Lnotti/5-Channel-High-Current-Li-po-Discharger/Solidworks/BoardV4.step

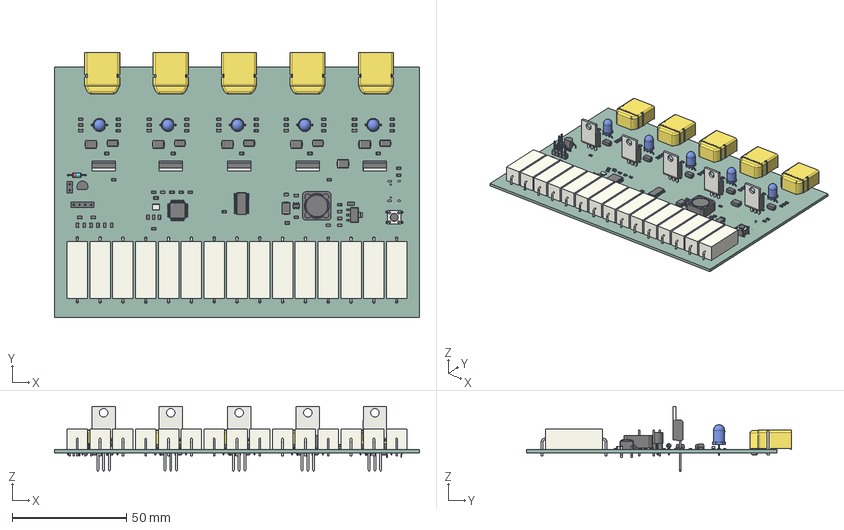
[picture p7: CAD file, 2026-05-29]
Solidworks/BoardV4.step
160.0 x 116.3 x 28.5 mm
C_0805_2012Metric x 23
XT60PW-M x 5
R_Axial_Power_L250mm_W90mm_P2794mm x 15
LED_D5.0mm-4_RGB_Wide_Pins x 5
R_0805_2012Metric x 44
D_SMB x 7
D_SMA x 5
SOT-223
TO-220-3_Vertical x 5
SW_PUSH_6mm
TO-92_Inline_Narrow
Crystal_SMD_3225-4Pin_3.2x2.5mm
PinHeader_1x04_P254mm_Vertical
LQFP-48_7x7mm_P0.5mm
Fuse_1206_3216Metric
SRR1260
TSOT-23-6
TSSOP-28_4.4x9.7mm_P0.65mm
D_DO-35_SOD27_P7.62mm_Horizontal
PinHeader_1x02_P254mm_Vertical
Lipo Discharger_PCB
