Lnotti/5-Channel-High-Current-Li-po-Discharger/Solidworks/CaseV1.0.SLDPRT

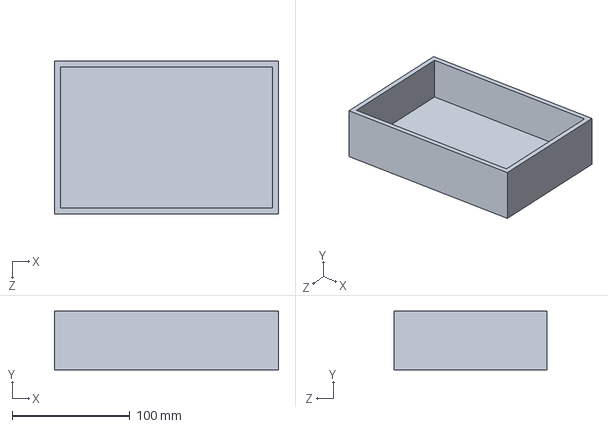
[picture p8: CAD file, 2026-05-29]
Solidworks/CaseV1.0.SLDPRT
190.0 x 50.0 x 130.0 mm
